yottatsa/card_barker/hp1661c/listing.jpg

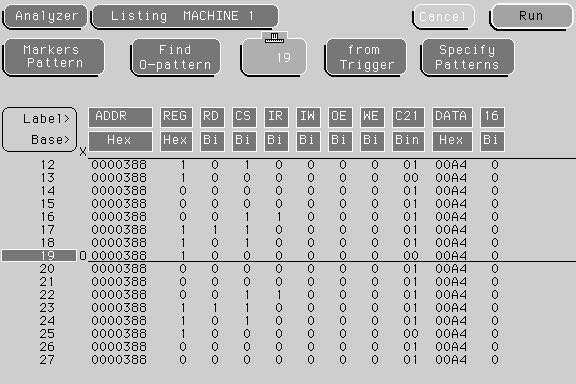
hp1661c/listing.jpg
