yottatsa/card_barker/win9x/sysprop-int.gif

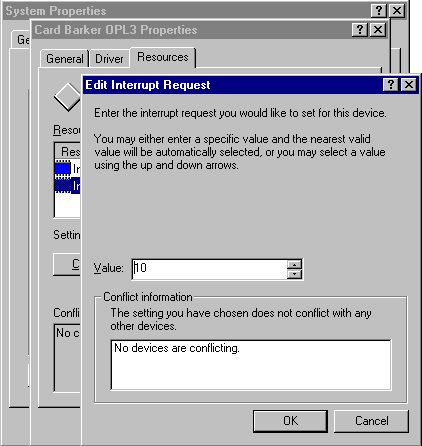
win9x/sysprop-int.gif
